eggsampler/WordWatch-hardware/ControllerBoard/plots/ControllerBoard__Assembly-1.png

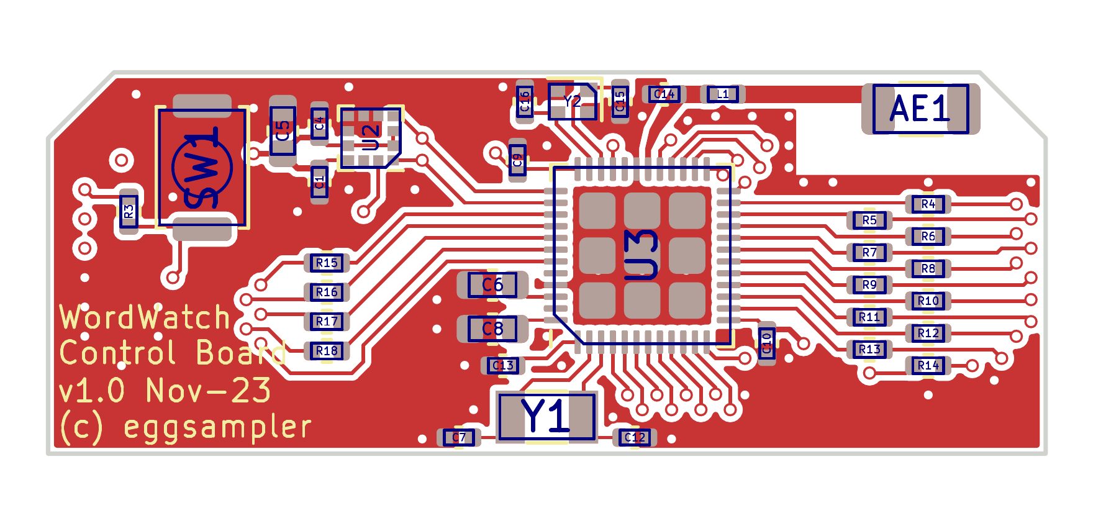
ControllerBoard/plots/ControllerBoard__Assembly-1.png
