eggsampler/WordWatch-hardware/ControllerBoard/plots/ControllerBoard__Assembly-2.png

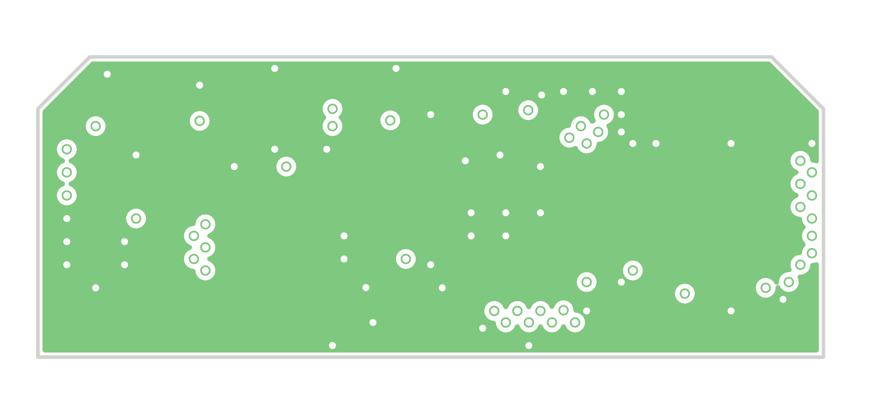
ControllerBoard/plots/ControllerBoard__Assembly-2.png
