eggsampler/WordWatch-hardware/ControllerBoard/plots/ControllerBoard__Assembly-4-flipped.png

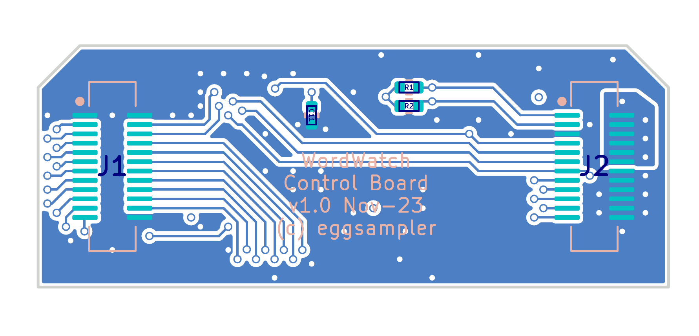
ControllerBoard/plots/ControllerBoard__Assembly-4-flipped.png
