eggsampler/WordWatch-hardware/ControllerBoard/plots/ControllerBoard__Assembly-4.png

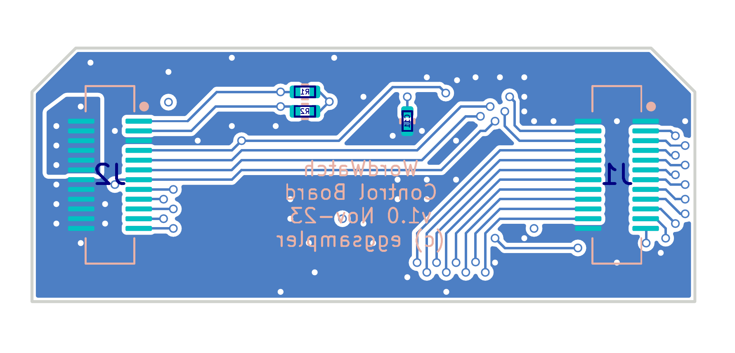
ControllerBoard/plots/ControllerBoard__Assembly-4.png
