eggsampler/WordWatch-hardware/LEDBoard/plots/LEDBoard__Assembly-1.png

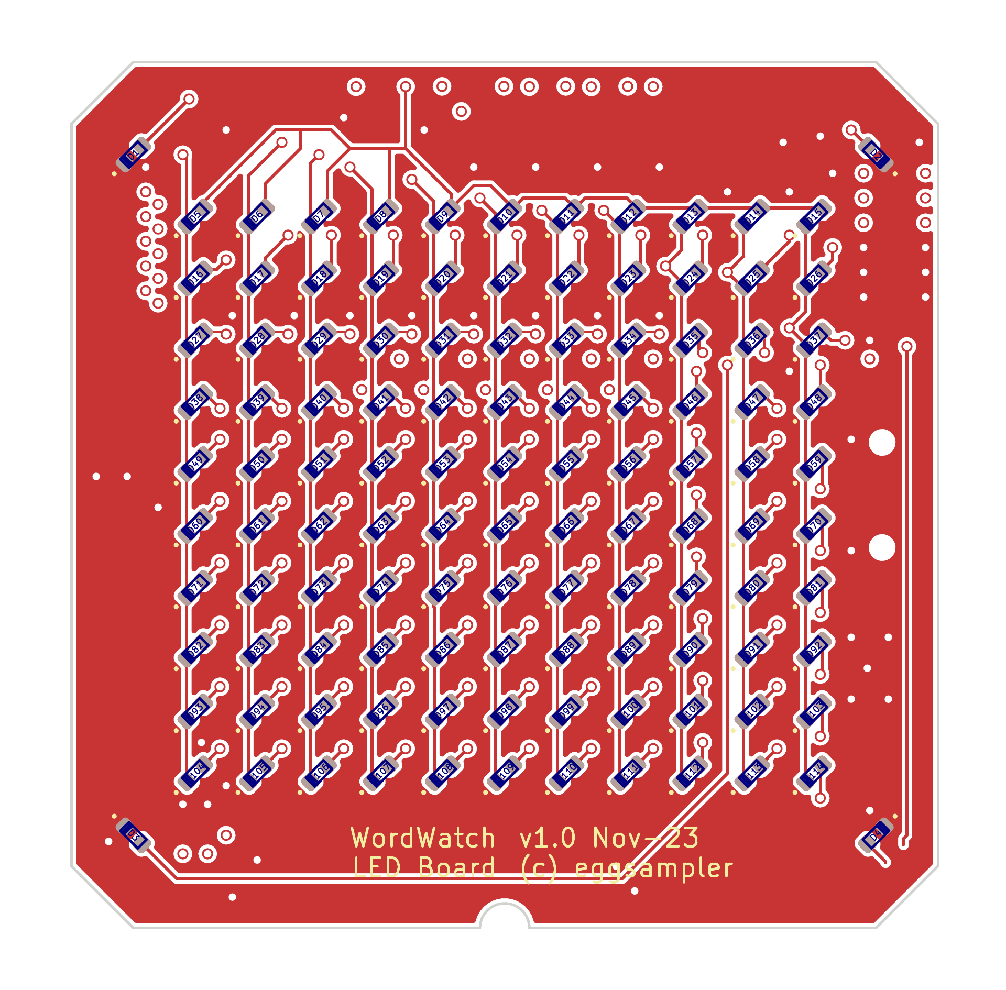
LEDBoard/plots/LEDBoard__Assembly-1.png
