eggsampler/WordWatch-hardware/LEDBoard/plots/LEDBoard__Assembly-2.png

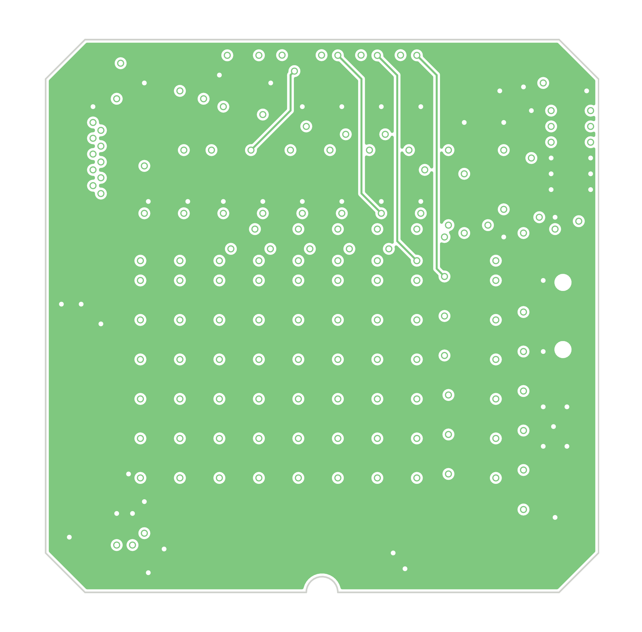
LEDBoard/plots/LEDBoard__Assembly-2.png
