eggsampler/WordWatch-hardware/LEDBoard/plots/LEDBoard__Assembly-3.png

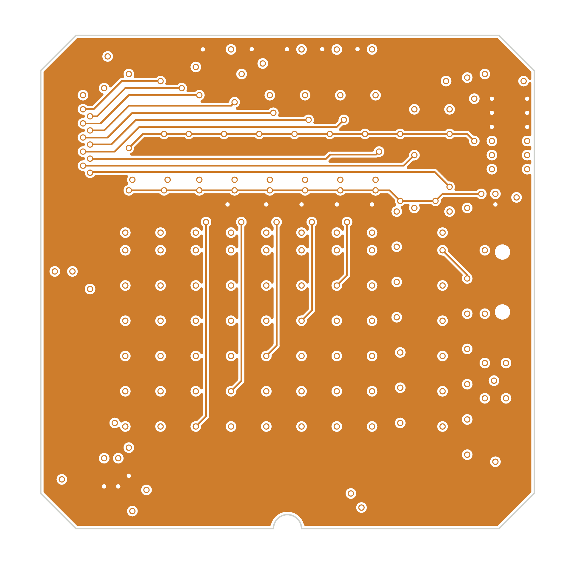
LEDBoard/plots/LEDBoard__Assembly-3.png
