eggsampler/WordWatch-hardware/LEDBoard/plots/LEDBoard__Assembly-4-flipped.png

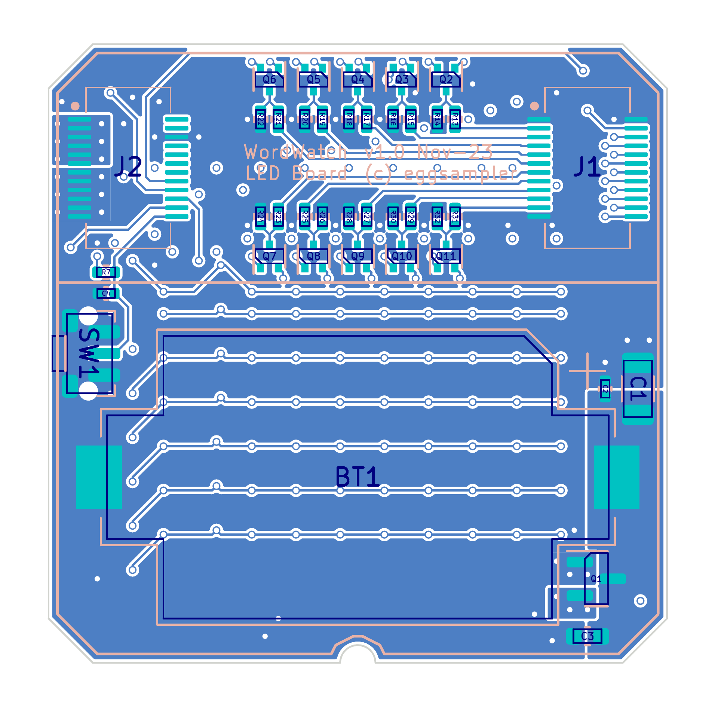
LEDBoard/plots/LEDBoard__Assembly-4-flipped.png
